strnadik/SlimeVR-SlimeCon/pictures/IMG_9833.jpg

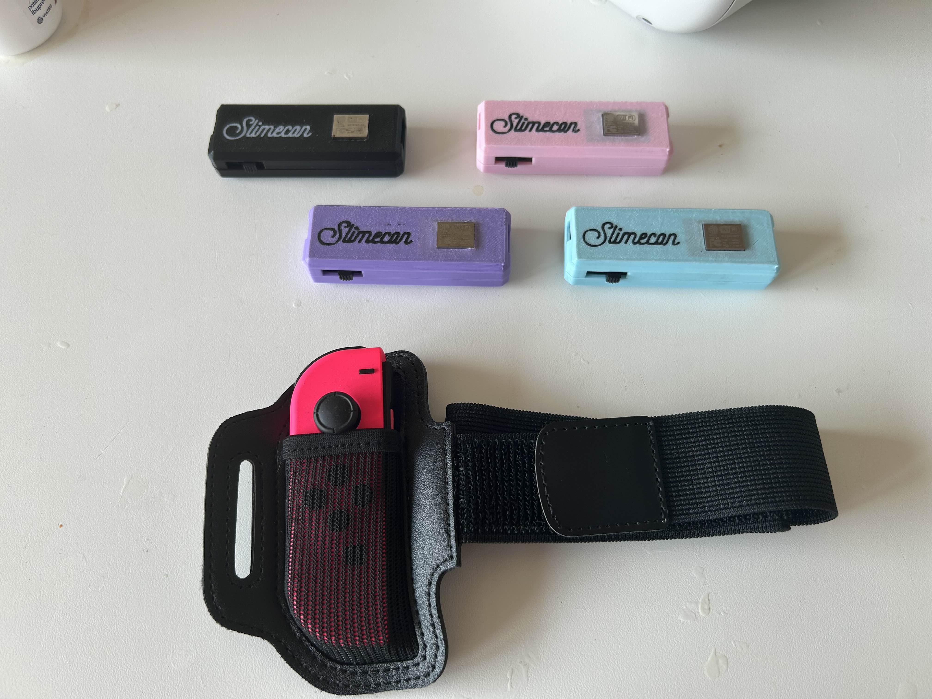
pictures/IMG_9833.jpg
