strnadik/SlimeVR-SlimeCon/pictures/IMG_9834.jpg

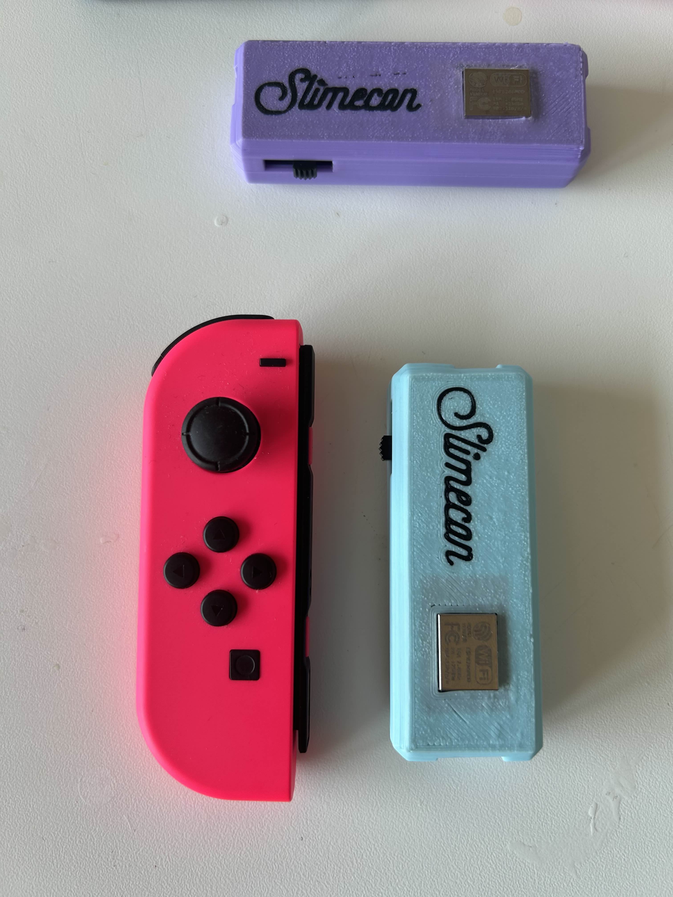
pictures/IMG_9834.jpg
